obones/OrangePiPower/LevelShifter.asc

M1: nmos; BSS88/SIE
Q1: npn; 2N3904
R1: res; 4.7k
R2: res; 1.5k
R3: res; 100k
R4: res; 6.8k
V1: voltage; 3.3
V2: voltage; 5
V3: voltage; PULSE(0 24 1 0.0001 0.0001 5 10 2)
Named nets: 0, PLoss3v3, PLoss5v, 24V
.tran 10
.lib siemens.lib
